rici029/project-fusion-smartwatch/pcb_bottom.png

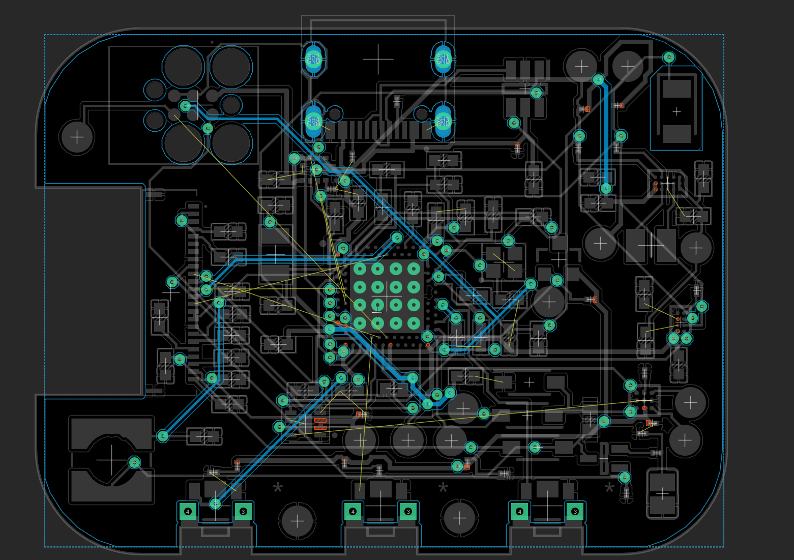
pcb_bottom.png
